DeppressedCabbage/Hephaestes38-zmk/PCB, Case/Case V2/Manufacturing/Hephaestus38v2 Switchplate.stp

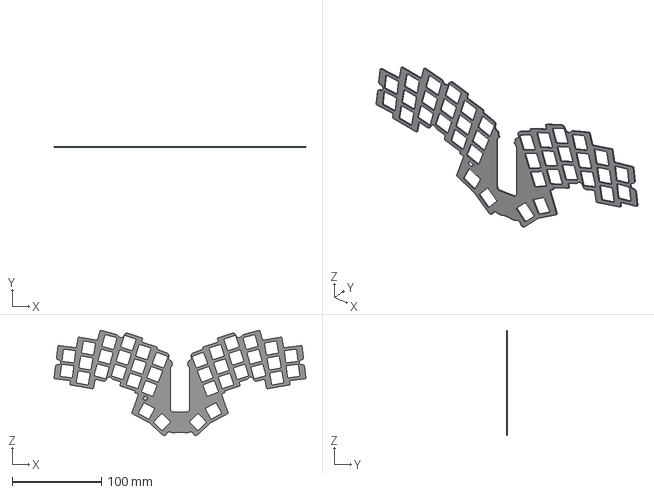
[picture p15: CAD file, 2025-11-24]
PCB, Case/Case V2/Manufacturing/Hephaestus38v2 Switchplate.stp
282.3 x 1.20 x 118.0 mm
